mattywausb/ElBanquos_AlarmClock/docs/Acknowledge.jpg

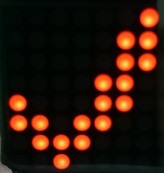
docs/Acknowledge.jpg
