mattywausb/ElBanquos_AlarmClock/docs/alrmoff01.jpg

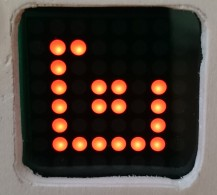
docs/alrmoff01.jpg
