mattywausb/ElBanquos_AlarmClock/docs/amplifire_mk1_proto.JPG

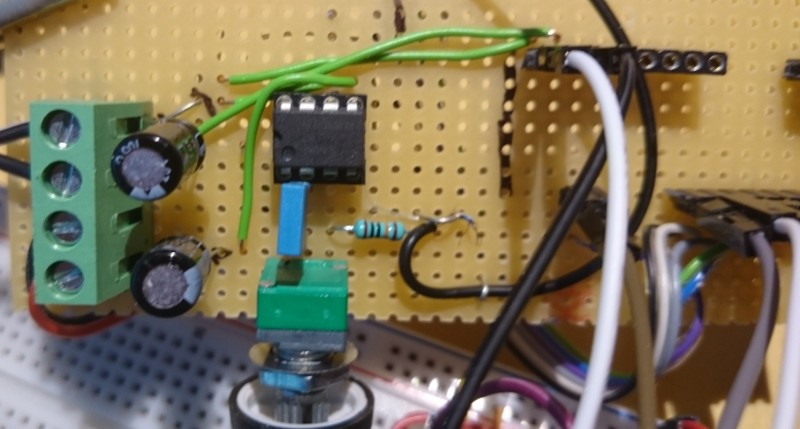
docs/amplifire_mk1_proto.JPG
