mattywausb/ElBanquos_AlarmClock/docs/amplifire_mk1_proto_bottom_side.JPG

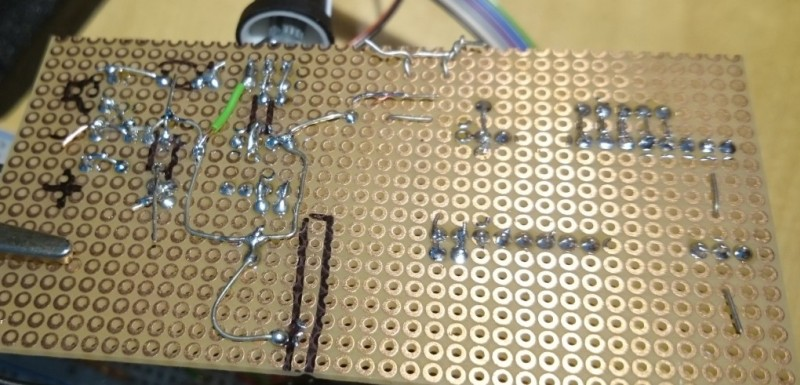
docs/amplifire_mk1_proto_bottom_side.JPG
