mattywausb/ElBanquos_AlarmClock/docs/Frontplate_before_mount.jpg

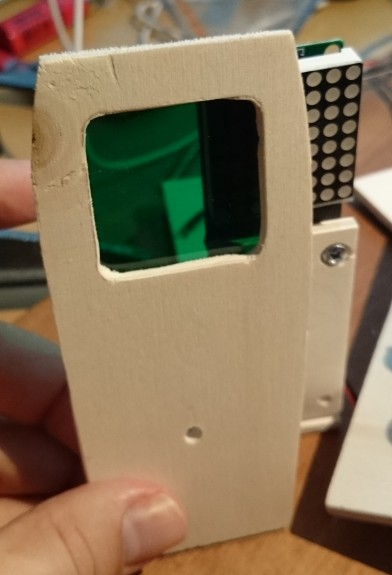
docs/Frontplate_before_mount.jpg
