mattywausb/ElBanquos_AlarmClock/docs/pcb_top_side.jpg

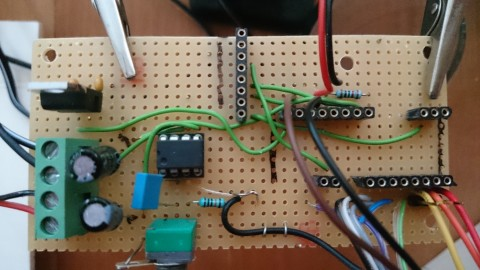
docs/pcb_top_side.jpg
