mattywausb/ElBanquos_AlarmClock/docs/Plug_to_led_matrix.jpg

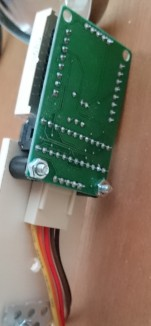
docs/Plug_to_led_matrix.jpg
