mattywausb/ElBanquos_AlarmClock/fritzing/alarmclock_mk1_Leiterplatte_all.png

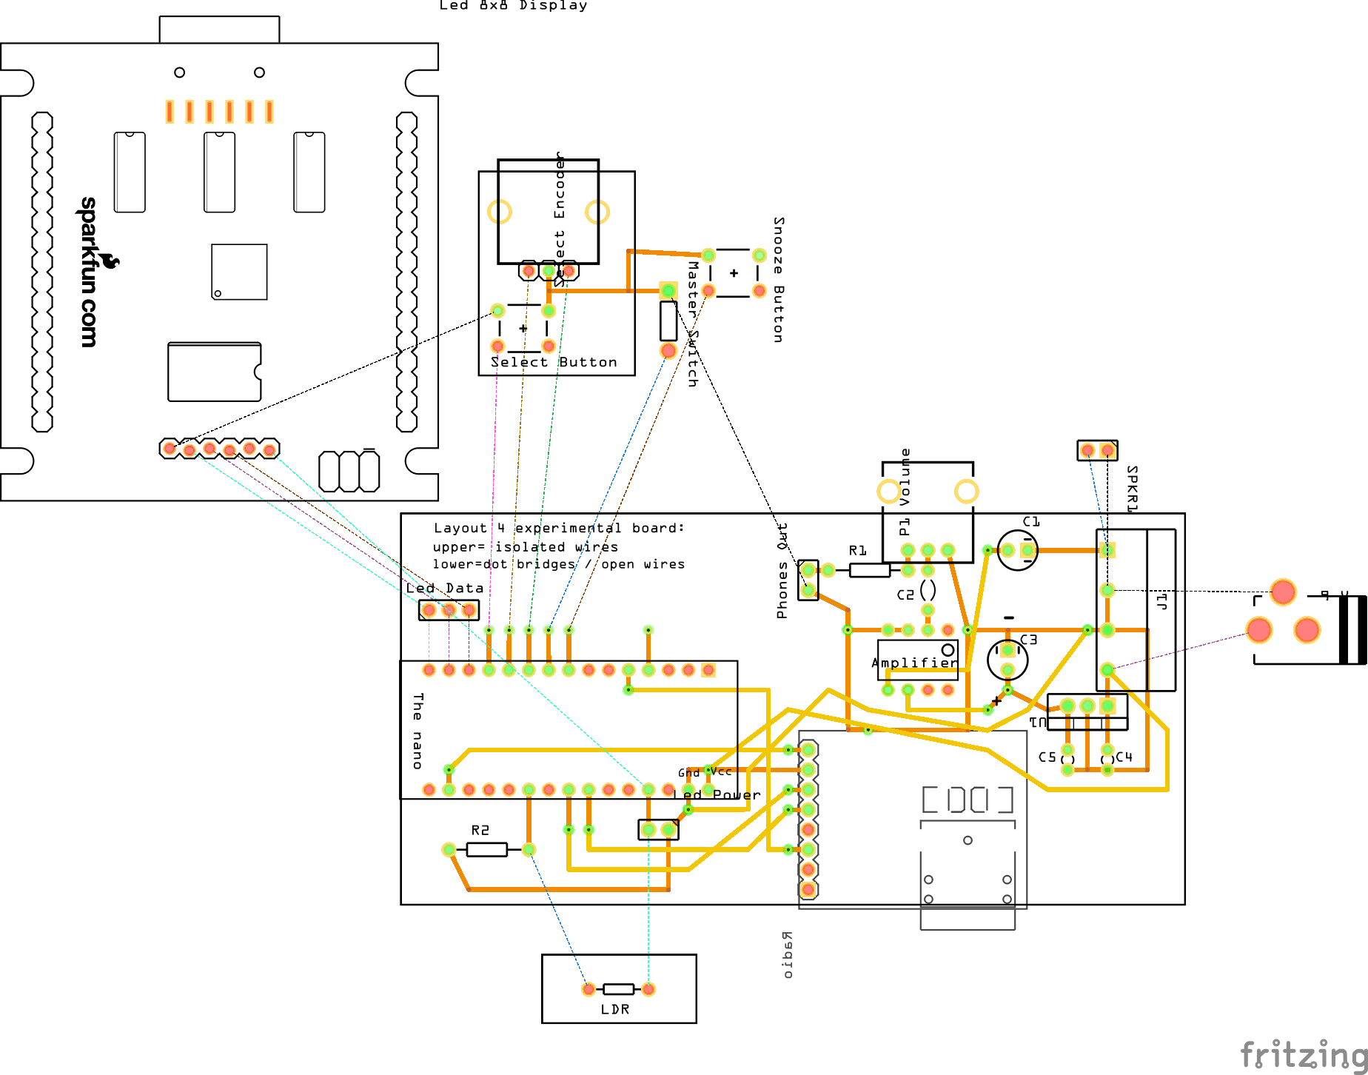
fritzing/alarmclock_mk1_Leiterplatte_all.png
