mattywausb/ElBanquos_AlarmClock/fritzing/alarmclock_mk1_Schaltplan.png

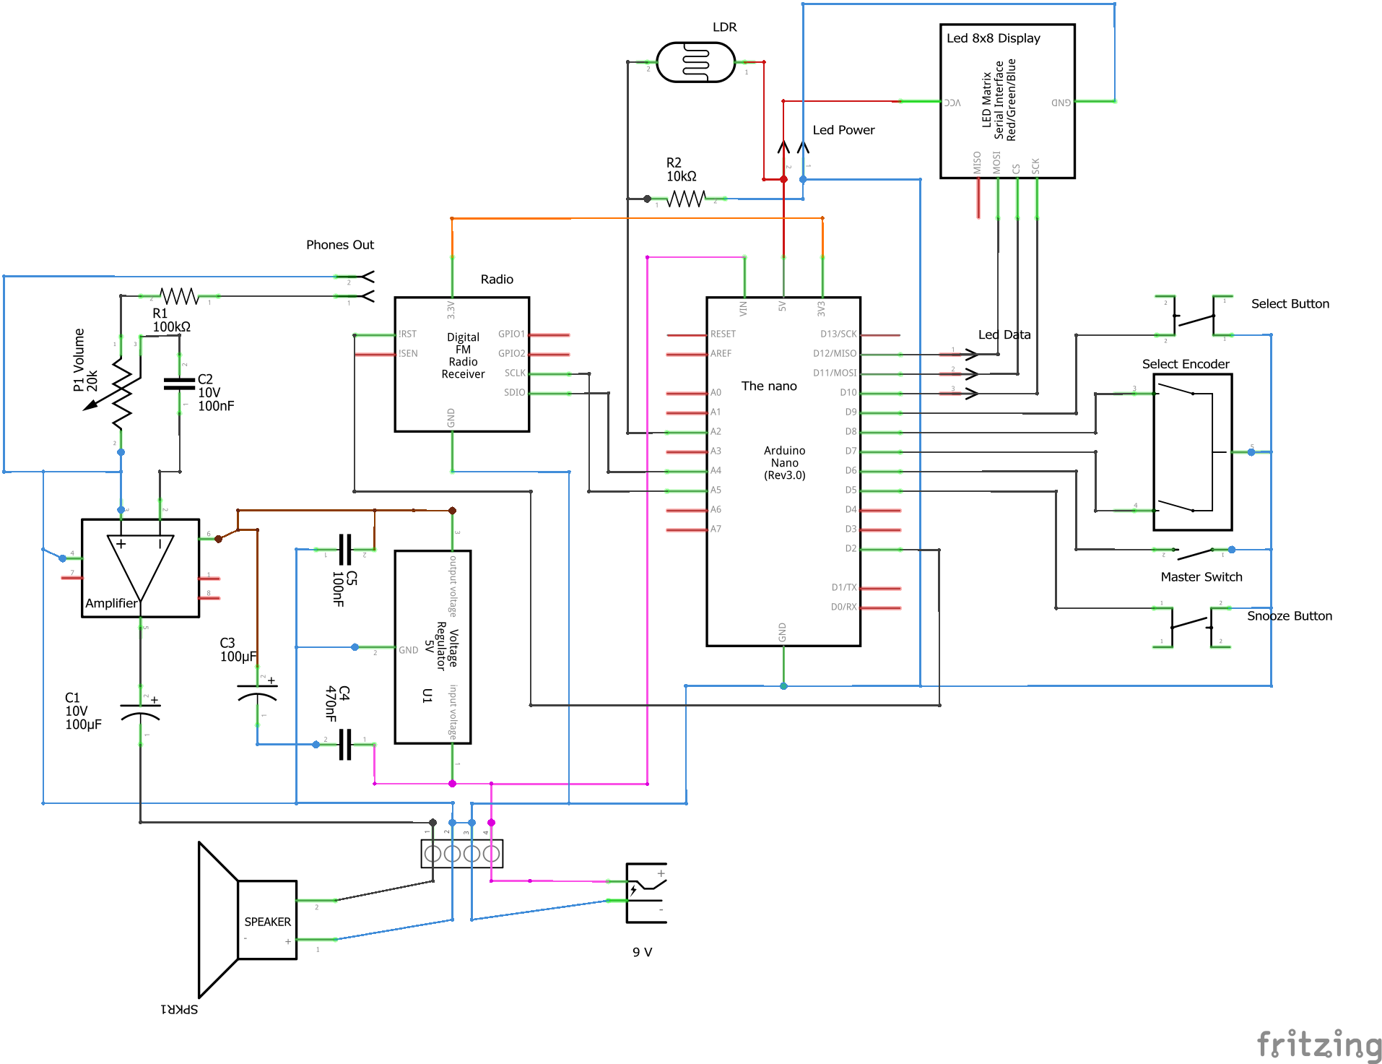
fritzing/alarmclock_mk1_Schaltplan.png
