mattywausb/ElBanquos_AlarmClock/fritzing/alarmclock_mk1_Steckplatine.png

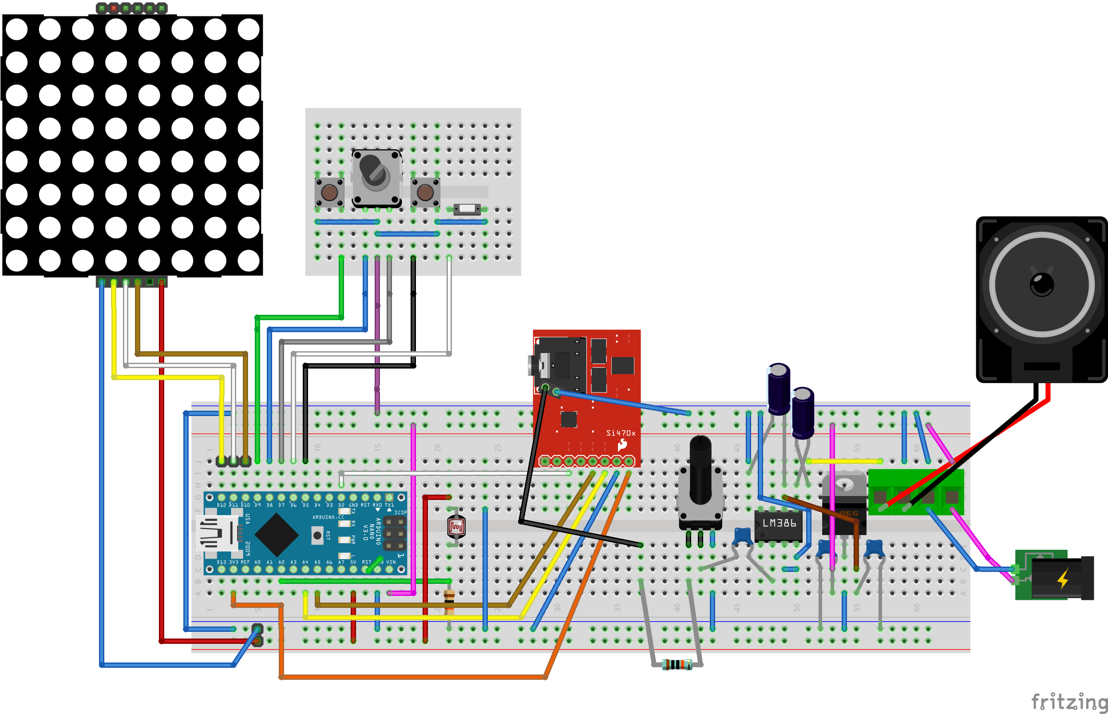
fritzing/alarmclock_mk1_Steckplatine.png
