mattywausb/ElBanquos_AlarmClock/docs/unmounted_setup.jpg

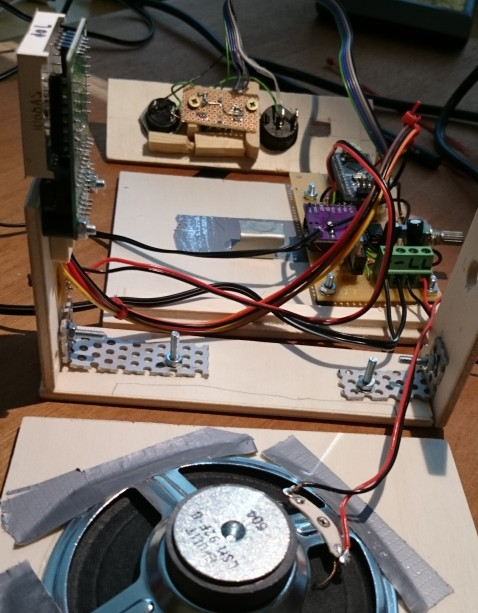
docs/unmounted_setup.jpg
